Lui831/Dart-Cannon/Semestre1/Esquemático Elétrico/Projeto_Microcontroladores.kicad_sch

## KiCad design Semestre1/Esquemático Elétrico/Projeto_Microcontroladores.kicad_sch (2024-06-02)

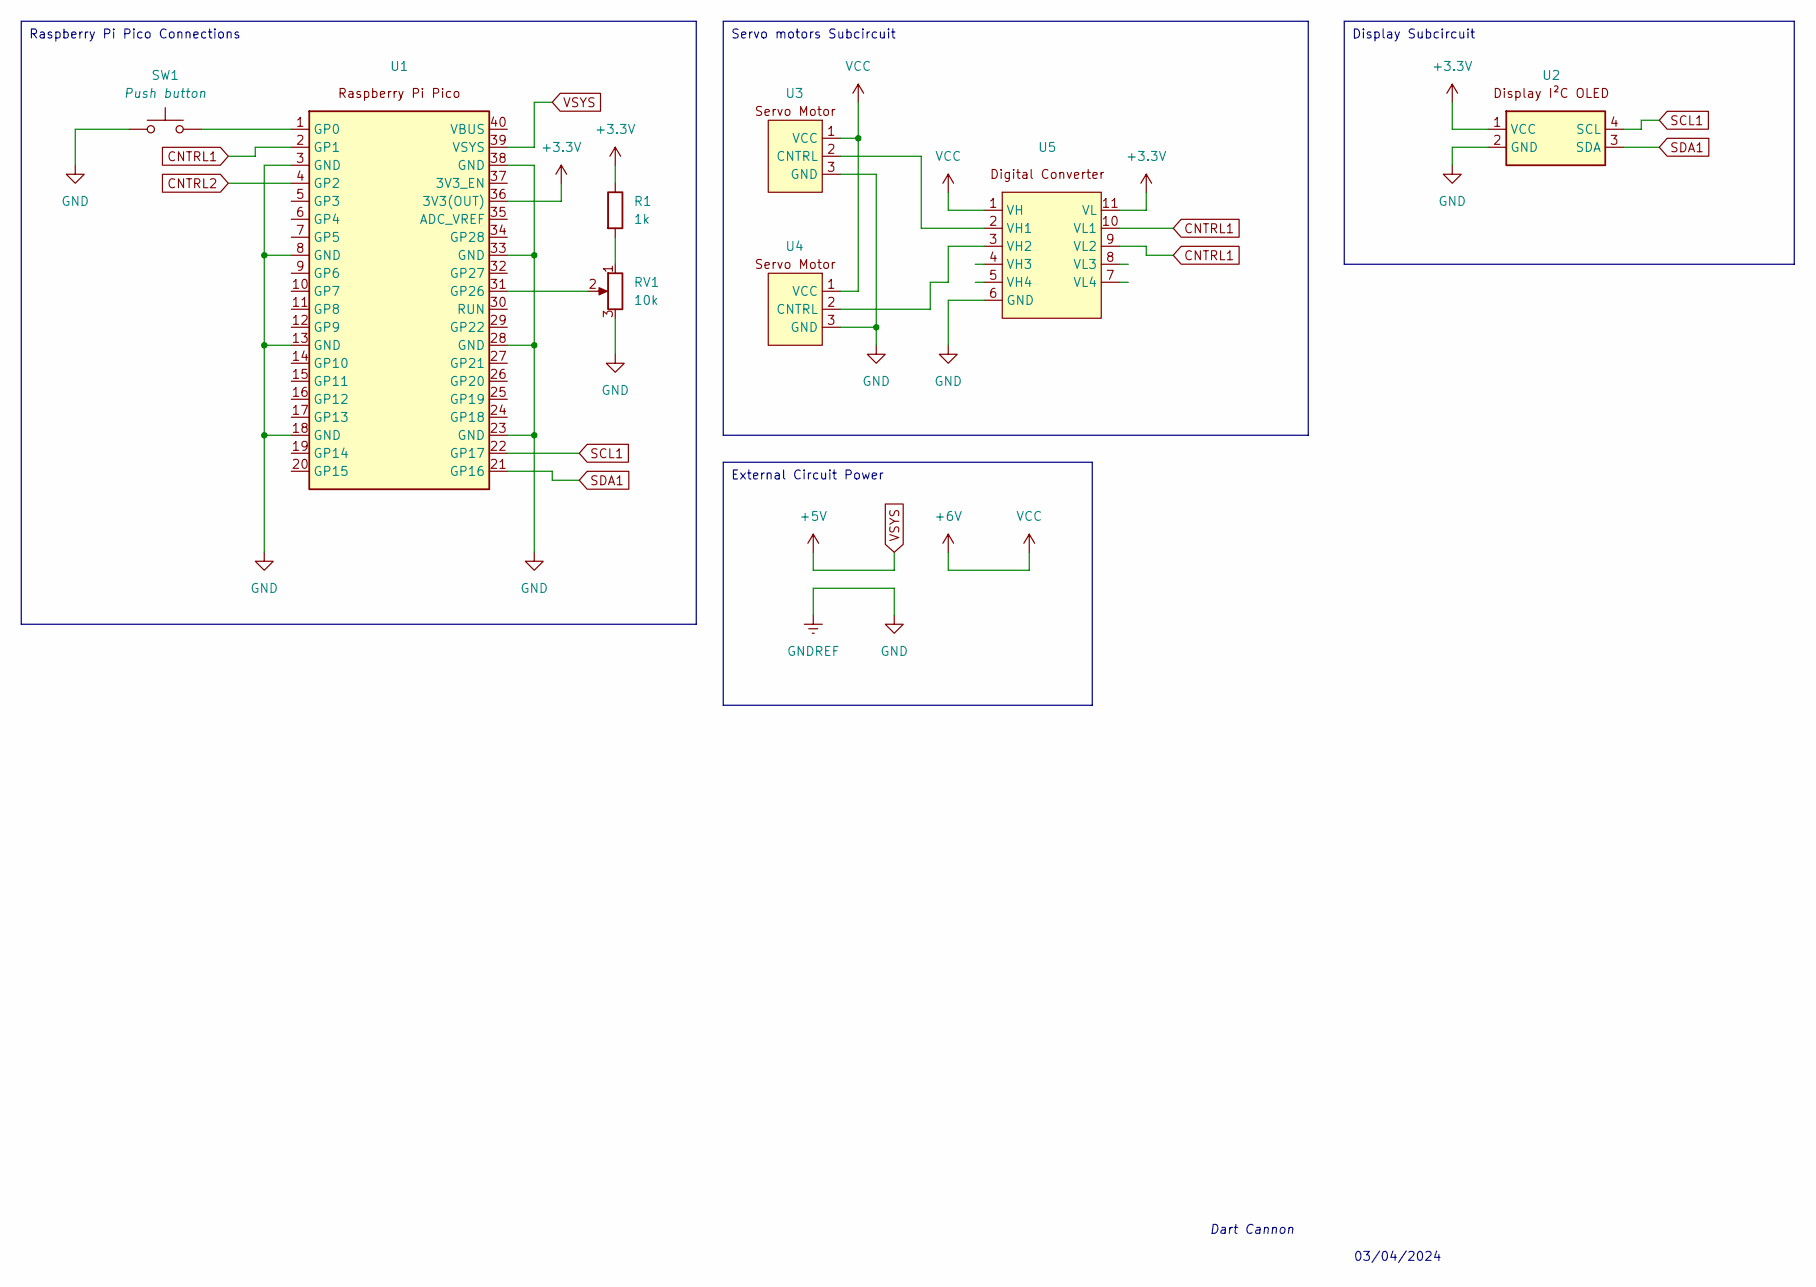
[picture p3: schematic Projeto_Microcontroladores.kicad_sch]

Parts:
R1: 1k
RV1: 10k
SW1: Push button
U1, U2, U3, U4, U5: (no value)

Connections:
+3.3V: R1.1, U1.36 (3V3(OUT)), U2.1 (VCC), U5.11 (VL)
+5V: U1.39 (VSYS)
+6V: U3.1 (VCC), U4.1 (VCC), U5.1 (VH)
CNTRL1: U1.2 (GP1), U5.9 (VL2), U5.10 (VL1)
CNTRL2: U1.4 (GP2)
GND: RV1.3, SW1.1, U1.3 (GND), U1.8 (GND), U1.13 (GND), U1.18 (GND), U1.23 (GND), U1.28 (GND), U1.33 (GND), U1.38 (GND), U2.2 (GND), U3.3 (GND), U4.3 (GND), U5.6 (GND)
unnamed: R1.2, RV1.1
unnamed: RV1.2, U1.31 (GP26)
unnamed: SW1.2, U1.1 (GP0)
unnamed: U3.2 (CNTRL), U5.2 (VH1)
unnamed: U4.2 (CNTRL), U5.3 (VH2)
SCL1: U1.22 (GP17), U2.4 (SCL)
SDA1: U1.21 (GP16), U2.3 (SDA)

Notes on the sheet:
External Circuit Power
Raspberry Pi Pico Connections
Servo motors Subcircuit
Display Subcircuit
Dart Cannon
03/04/2024
